tonykim07/fNIRS/firmware/STM32/fNIRS/Core/Inc/main.h

#define SD_CARD_DETECT_Pin GPIO_PIN_13
#define SD_CARD_DETECT_GPIO_Port GPIOC
#define PWM_CTRL_EN1_Pin GPIO_PIN_7
#define PWM_CTRL_EN1_GPIO_Port GPIOC
#define MCU_TEST_LED_Pin GPIO_PIN_8
#define MCU_TEST_LED_GPIO_Port GPIOA
#define SPI_CS2_Pin GPIO_PIN_9
#define SPI_CS2_GPIO_Port GPIOA
#define SPI_CS1_Pin GPIO_PIN_10
#define SPI_CS1_GPIO_Port GPIOA
