tonykim07/fNIRS/software/config.py

"""
config.py
===================
This configuration file contains constants and settings that are used throughout the software.
"""

# Path to your USB‑serial device
SERIAL_PORT = '/dev/tty.usbmodem205E386D47311'

# Serial settings
BAUD_RATE = 9600
TIMEOUT   = 0.01
