tonykim07/fNIRS/firmware/STM32/fNIRS/Core/Inc/isr.h

#ifndef INC_ISR_H_
#define INC_ISR_H_

/* INCLUDES */
#include "main.h"
#include <stdbool.h>

/* DEFINES */

/* DATA STRUCTURES */
typedef struct
{
    uint16_t tim4_timer_ticks;
    bool emitter_control_timer_flag;
} isr_vars_S;

/* FUNCTION DECLARATIONS */
uint16_t isr_get_1khz_timer_ticks(void);
bool isr_get_emitter_control_timer_flag(void);
void isr_reset_emitter_control_timer_flag(void);

#endif /* INC_ISR_H_ */
